rothdu/EEE4113F-Group13-2024/final-report/FrontMatter/Title.tex

\thispagestyle{empty}
\begin{center}
    
\Huge

\vspace{5cm}

% Title
EEE4113F 2024 Final Report \\
Red-winged Starling Nest Monitoring System

\vspace{2.5cm}

% UCT logo
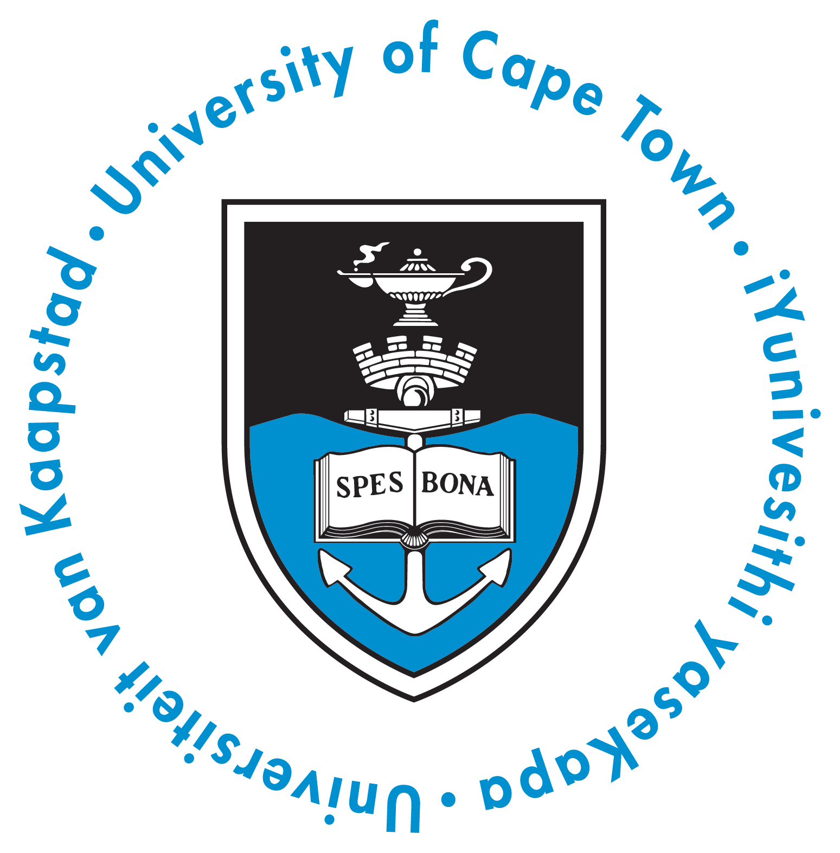
[picture p15: final-report/FrontMatter/UCT_logo.png]


\vfill

% My name
\large
\textbf{Prepared by:}\\
\textit{Group 13} \\
Ruviel Perumal - Power\\
Thiyashan Pillay - Electronic hardware \\
Robert Dugmore - Firmware\\
Mathapelo Morobi - Mechanical casing\\

\vspace{1cm}

% My supervisor's name
\textbf{Prepared for:}\\
EEE4113F\\
Department of Electrical Engineering\\
University of Cape Town

\vspace{2cm}

% Today's date
\today

% To add keywords?
% \vspace{2cm}
% \textbf{Keywords:} Keywords here

\end{center}
