rothdu/EEE4113F-Group13-2024/final-report/FrontMatter/Abstract.tex

\documentclass[class=report,11pt,crop=false]{standalone}
\input{../Style/ChapterStyle.tex}
\input{../FrontMatter/Glossary.tex}
\begin{document}
% \afterpage{
% \newgeometry{margin=30mm}
\chapter*{Abstract}

\ifstandalone
% \bibliography{../Bibliography/References.bib}
% \printnoidxglossary[type=\acronymtype,nonumberlist]
\fi
\end{document}
