rothdu/EEE4113F-Group13-2024/final-report/FrontMatter/Acknowledgements.tex

\documentclass[class=report,11pt,crop=false]{standalone}
\input{../Style/ChapterStyle.tex}
\begin{document}
\chapter*{Acknowledgements}
% \epigraph{No man is an island entire of itself; every man is a piece of the continent, a part of the main.}%
    % {\emph{---John Donne}}
% \vspace{0.3cm}

% Financial

% Academic

% Friends

% Family

\end{document}
