rothdu/EEE4113F-Group13-2024/final-report/Main.tex

% !TeX root = Main.tex

\documentclass[11pt]{report}
\input{Style/ChapterStyle.tex}
\usepackage{standalone} % Best loaded last in the preamble

% \input{FrontMatter/Glossary.tex}

\begin{document}

\pagenumbering{roman}
\input{FrontMatter/Title.tex}
\input{FrontMatter/Declaration.tex}
% \input{FrontMatter/Acknowledgements.tex}
% \input{FrontMatter/Abstract.tex}
\glsresetall

\tableofcontents
% \listoffigures

% \printnoidxglossary[type=\acronymtype,nonumberlist,title={Abbreviations}]
\newpage

\pagenumbering{arabic}

\input{Chapters/Introduction.tex}
\input{Chapters/Problem-analysis.tex}
\input{Chapters/Literature.tex}
\input{Chapters/Power.tex}
\input{Chapters/Hardware.tex}
\input{Chapters/Firmware.tex}
\input{Chapters/Mechanical.tex}
\input{Chapters/Conclusions.tex}
\input{Chapters/Recommendations.tex}

\newpage
\bibliography{Bibliography/References.bib}

\appendix
\input{Appendices/Appendix-A1.tex}
\input{Appendices/Appendix-B1.tex}

\end{document}
