rothdu/EEE4113F-Group13-2024/final-report/Chapters/Introduction.tex

% ----------------------------------------------------
% Introduction
% ----------------------------------------------------
\documentclass[class=report,11pt,crop=false]{standalone}
\input{../Style/ChapterStyle.tex}
\input{../FrontMatter/Glossary.tex}
\begin{document}
\chapter{Introduction \label{ch:introduction}}
% ----------------------------------------------------

\section{Background}
\section{Background}
The FitzPatrick Institute of African Ornithology falls within the Department of Biological Sciences at the University of Cape Town (UCT) in South Africa. It is a non-profit organisation that established it’s affiliation with UCT in September 1959. The main aim of FitzPatrick is to deepen understanding of avian life and to establish a permanent repository for ornithological data and materials crucial for research. They serve as pioneers and are one of the leading institutes when it comes to the studies of birds in the Southern Hemisphere.
\newline

The FitzPatrick Institute is also committed to training the next generation of ornithologists and conservationists. It offers undergraduate and postgraduate programs in ornithology, providing students with hands-on research experience and mentorship from leading experts in the field.
\newline

Overall, the FitzPatrick Institute of African Ornithology stands as a beacon of excellence in avian research and conservation, contributing valuable insights to our understanding of bird biology and ecology while working tirelessly to ensure the continued survival of Africa's avian biodiversity.
\newline

In 2017, the FitzPatrick initiated the Red-winged Starling Urban Ecology Project. The Red-winged starling, scientifically termed Onychognathus morio, is a notable bird within the Sturnidae family, endemic to eastern Africa from Ethiopia to South Africa's Cape region. For this specific project, we worked with Sally, who does her research on these starling birds.
\newline

Her main problems along her researching career were not being able to understand exactly what is going on in these nests of the Starling birds. Hence, her need for a camera trap device so that she can have more accurate and efficient data.

%%\section{Objectives}

%%\section{System Requirements}

\section{Scope \& Limitations}
The project focused on developing a remote surveillance system for the Starlings bird population at the University of Cape Town (UCT), which was divided into four main subsections: Power, Hardware, Firmware, and Mechanical Casing. the project aimed to develop a technological design to assist in wildlife data collection and conservation. This endeavour involved a collaborative effort including various engineering disciplines and leveraging the vast knowledge and research capabilities of the Fitz Patrick Institute.
\newline
Over 7 weeks, the project encompassed stakeholder engagement for gathering requirements, the design process, iterative improvements, and thorough testing. Material procurement was conducted from limited electronics online stores, with shipping days taking long and physical visits to outlets like BUCO for items not available online. A budget of R2000 was allocated to ensure a cost-effective solution.
\newline

In the subsequent chapters, the design processes of each submodule will be explained, showcasing diverse expertise and innovative solutions tailored to the unique requirements of monitoring the Starlings bird population. 

\section{Report Outline}
The report will proceed in a structured manner to provide a comprehensive analysis and solution to the identified problem. Beginning with the Introduction, the report will establish the context and significance of the problem, setting the stage for subsequent chapters. Following this, the Problem Analysis section will delve into a detailed examination of the identified issue, analysing its implications and significance within the relevant context.
\newline

Subsequently, a Literature Review will be conducted to draw upon existing research and scholarly work related to the problem statement. This review will serve to establish a theoretical framework and deepen understanding of the topic. Moving forward, chapters dedicated to Power, Hardware, Mechanical, and Firmware will follow. Each chapter will offer an overview of its respective aspect, analysing requirements, considerations, and design strategies pertinent to the solution.
\newline

The Conclusions section will summarise key findings and insights drawn from the analysis, offering recommendations for future actions and areas of further research. References will be provided to acknowledge and cite sources utilized throughout the report.
\newline
Finally, the report includes two appendices. Appendix A, the main appendix, contain supplementary information, data, or detailed analyses to support the main body of the report. Appendix B, consists of the GAs completed by each member of Group 13.

% ----------------------------------------------------
\ifstandalone
\bibliography{../Bibliography/References.bib}
\printnoidxglossary[type=\acronymtype,nonumberlist]
\fi
\end{document}
% ----------------------------------------------------
