rothdu/EEE4113F-Group13-2024/final-report/FrontMatter/Declaration.tex

{
\onehalfspacing
   
% Please leave the declaration as it is (Standard UCT declaration).
\chapter*{Declaration}
% \hrule

\vskip 10mm
\begin{enumerate}
\item I know that plagiarism is wrong. Plagiarism is to use another's work and pretend that it is one's
own.
\item I have used the IEEE convention for citation and referencing. Each contribution to, and quotation in,
this report from the work(s) of other people has been attributed, and has been cited and
referenced.
\item This report is my own work.
\item I have not allowed, and will not allow, anyone to copy my work with the intention of passing it off
as their own work or part thereof.
\end{enumerate}
\vskip 30mm

%signatures
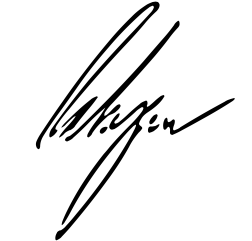
[picture p16: final-report/signatures/DGMROB001.png]
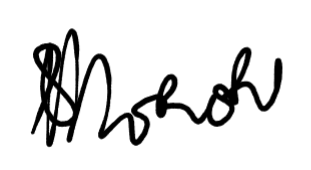
[picture p17: final-report/signatures/MRBMAT004.png]
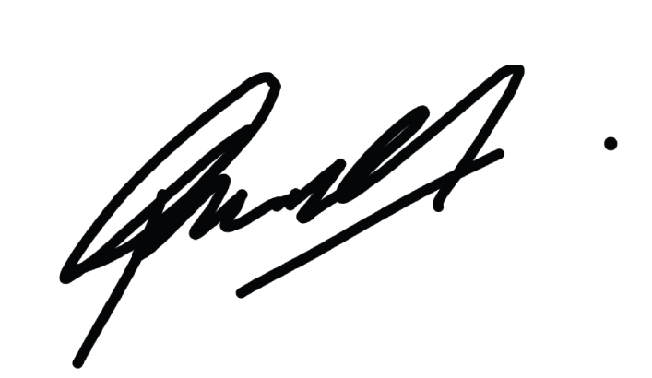
[picture p18: final-report/signatures/PRMRUV001.png]
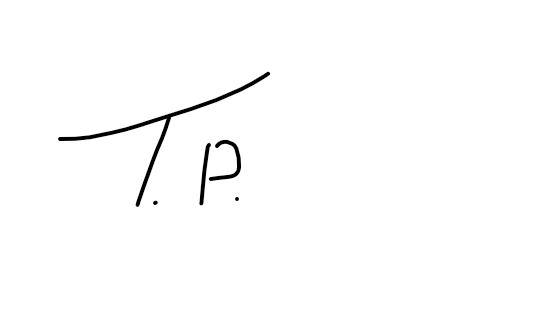
[picture p19: final-report/signatures/PLLTHI032.png]
\par\noindent\makebox[1.3in]{}\hfill\makebox[1.3in]{}\hfill\makebox[1.2in]{}\hfill\makebox[1.3in]{}%

%lines
\par\noindent\makebox[1.3in]{\hrulefill}\hfill\makebox[1.3in]{\hrulefill}\hfill\makebox[1.3in]{\hrulefill}\hfill\makebox[1.3in]{\hrulefill}%

%names
\par\noindent\makebox[1.3in][c]{Robert Dugmore}\hfill\makebox[1.3in][c]{Mathapelo Morobi}\hfill\makebox[1.3in][c]{Ruviel Perumal}\hfill\makebox[1.3in][c]{Thiyashan Pillay}

\vskip 20mm

%date
\par\noindent\makebox[1.3in]{\today}
\par\noindent\makebox[1.3in]{\hrulefill}
\par\noindent\makebox[1.3in][c]{Date}

% use for single signature:
% \par\noindent\makebox[2.0in]{\includegraphics[width=0.2\linewidth]{signatures/DGMROB001.png}}\hfill\makebox[2.0in]{\today}%
% \par\noindent\makebox[2.0in]{\hrulefill} \hfill\makebox[2.0in]{\hrulefill}%
% \par\noindent\makebox[2.0in][l]{Robert Dugmore}      \hfill\makebox[2.0in][l]{Date}%

}
