rothdu/EEE4113F-Group13-2024/final-report/Images/ESP-flow.png

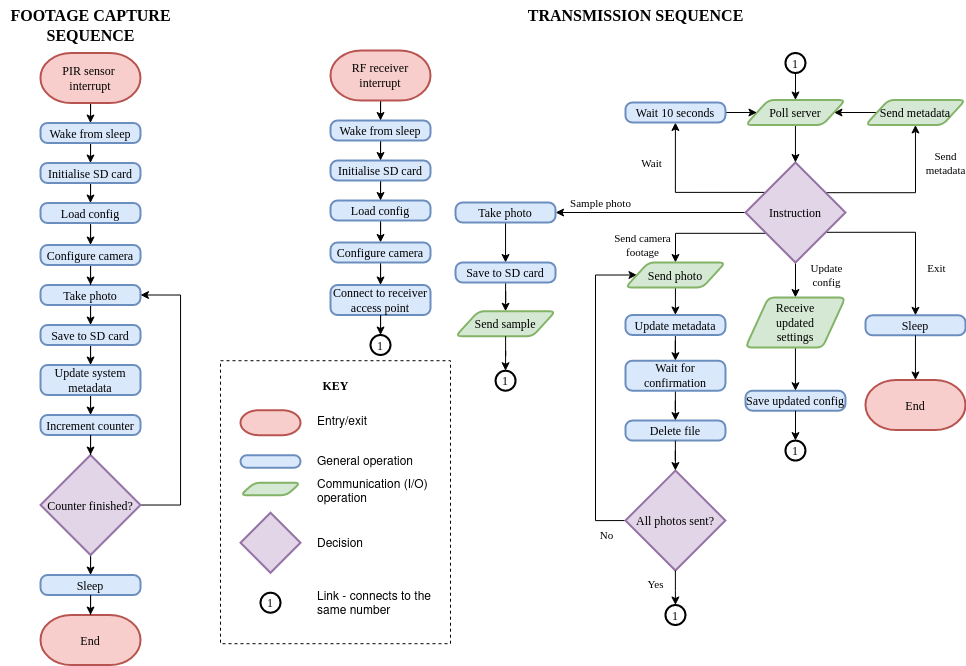
final-report/Images/ESP-flow.png
