rothdu/EEE4113F-Group13-2024/final-report/Images/flowchart.png

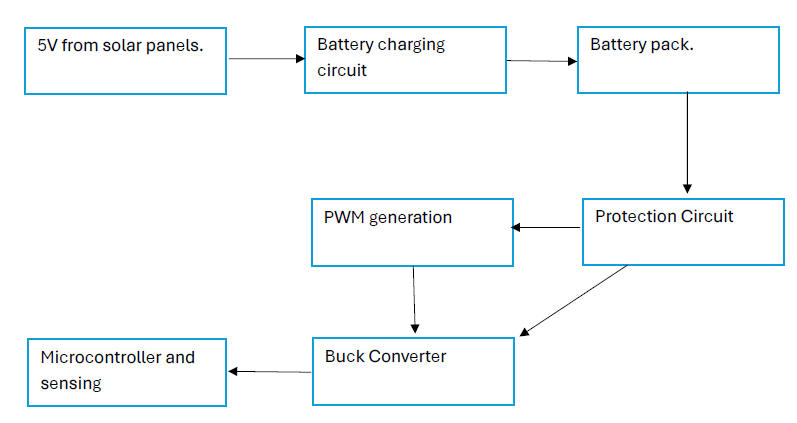
final-report/Images/flowchart.png
