rothdu/EEE4113F-Group13-2024/final-report/Images/nest.png

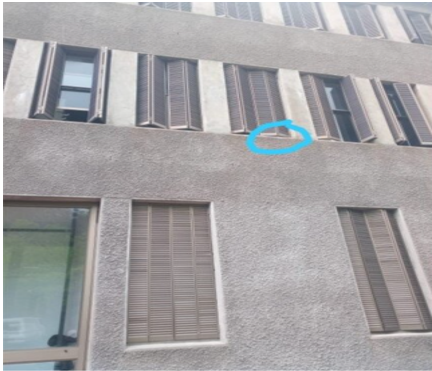
final-report/Images/nest.png
