rothdu/EEE4113F-Group13-2024/final-report/Images/sample-image-firmware.jpeg

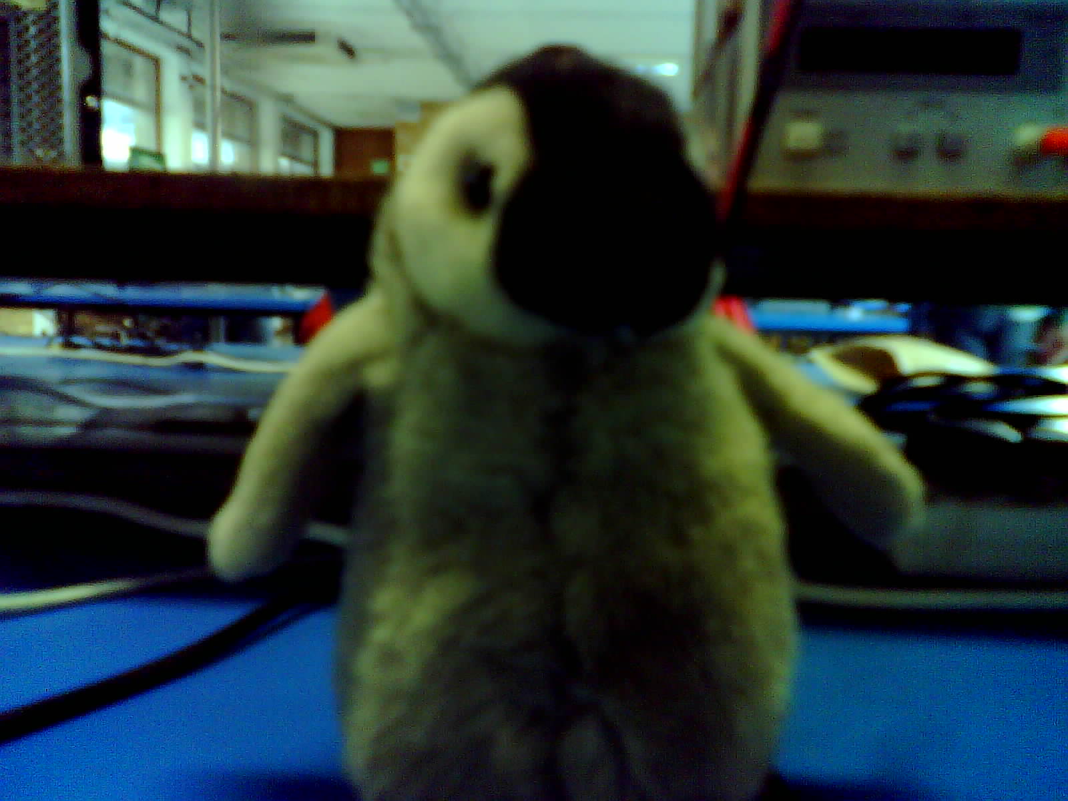
final-report/Images/sample-image-firmware.jpeg
