rothdu/EEE4113F-Group13-2024/final-report/Images/sensor_ss.png

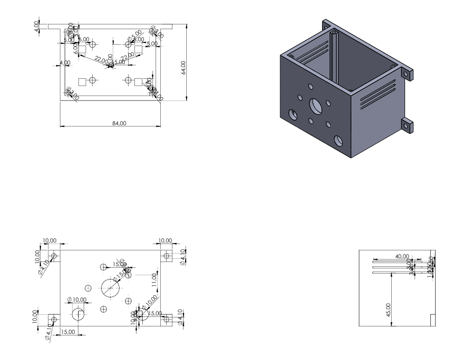
final-report/Images/sensor_ss.png
