rothdu/EEE4113F-Group13-2024/final-report/Images/stakeholdermap.jpeg

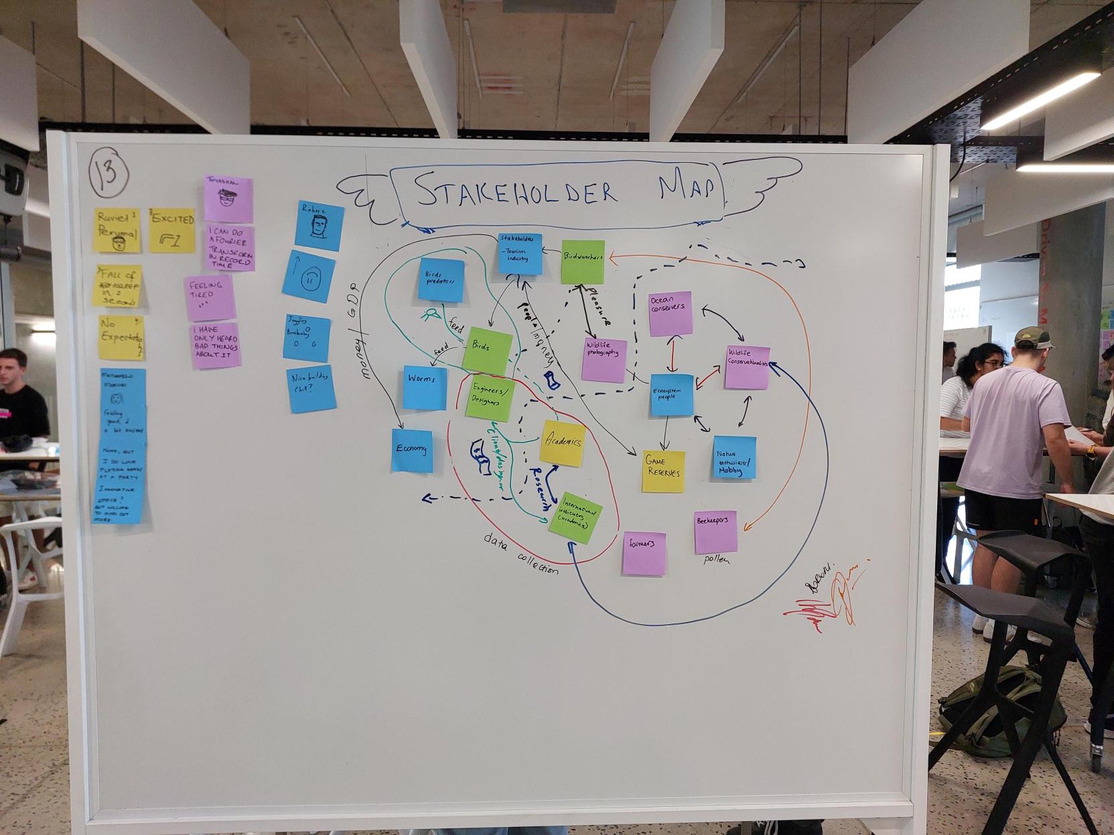
final-report/Images/stakeholdermap.jpeg
