rothdu/EEE4113F-Group13-2024/final-report/Images/ui.jpeg

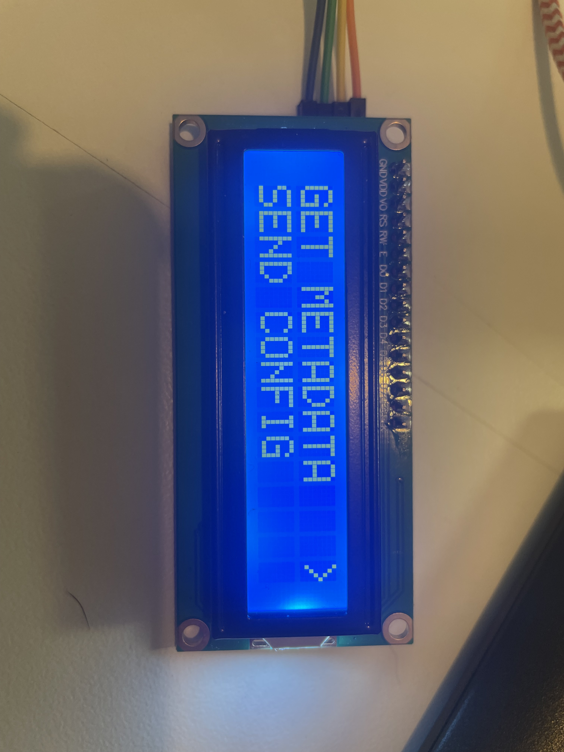
final-report/Images/ui.jpeg
