rothdu/EEE4113F-Group13-2024/sample-photos/2.jpeg

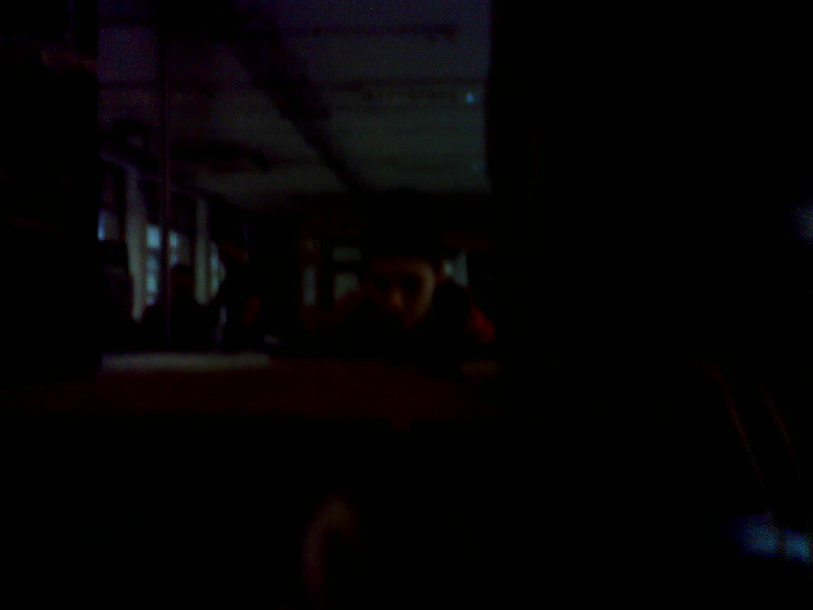
sample-photos/2.jpeg
