rothdu/EEE4113F-Group13-2024/sample-photos/3.jpeg

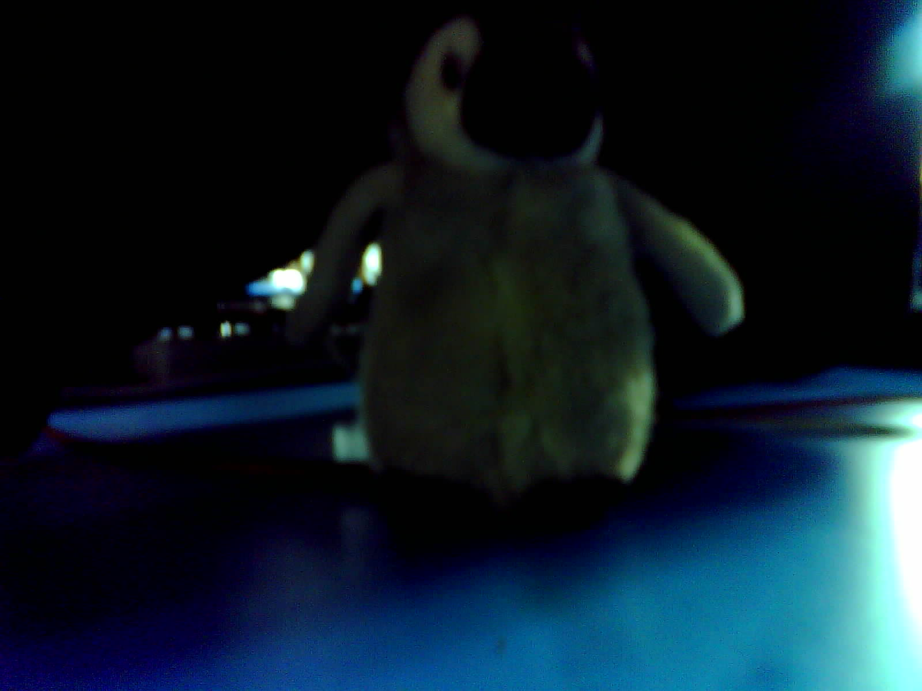
sample-photos/3.jpeg
