rothdu/EEE4113F-Group13-2024/circuit-schematics/LDR_Circuit.asc

LDR: res; 18k
M1: nmos
R1: res; 22k
R2: res; 22k
R3: res; 22k
R4: res; 3.3k
R5: res; 22k
U1: opamp2; LM358
V1: voltage; 5
V2: voltage; 3.3
Named nets: Out, 0, V++, VCC, Vin
.lib lm358.lib
.tran 0.01
