rothdu/EEE4113F-Group13-2024/circuit-schematics/LED_Circuit.asc

D1: LED
D2: LED
D3: LED
D4: LED
D5: LED
Q1: npn; 2N2222
R1: res; 10k
R2: res; 18k
R3: res; 15
R4: res; 280
V1: voltage; 5
V2: voltage; 3.3
V3: voltage; 5V
Named nets: 0
.tran 10
