rothdu/EEE4113F-Group13-2024/circuit-schematics/PNP_Switch.asc

Q1: pnp; 2N2907
R1: res; 1k
R2: res; 10k
R3: res; 22k
Named nets: 0, Out, ESP_In, Sensor_In
.tran 1
