rothdu/EEE4113F-Group13-2024/circuit-schematics/EEE4113F_Power_Submodule_Group13.kicad_sch

## KiCad design circuit-schematics/EEE4113F_Power_Submodule_Group13.kicad_sch (2024-05-12)

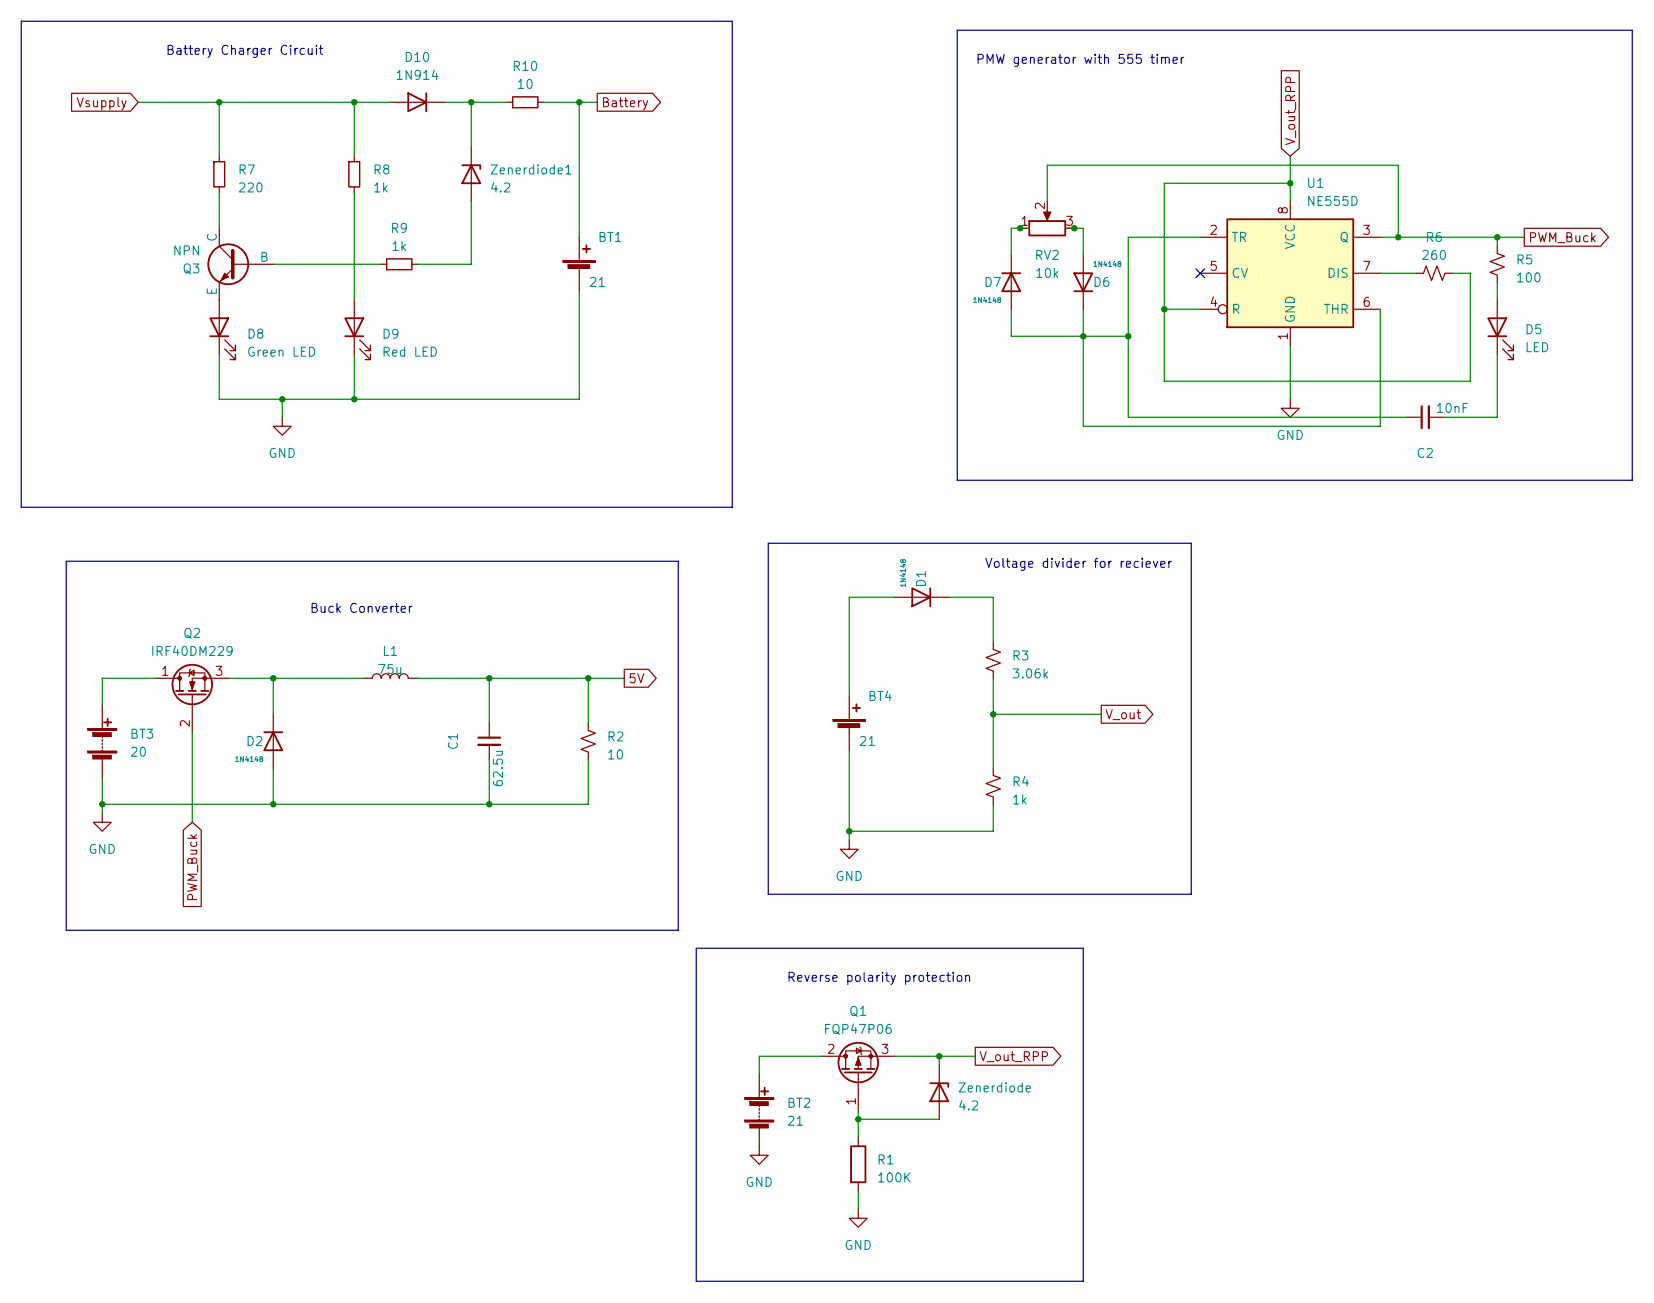
[picture p35: schematic EEE4113F_Power_Submodule_Group13.kicad_sch]

Parts:
BT1, BT2, BT4: 21
BT3: 20
C1: 62.5u
C2: 10nF
D1, D2, D6, D7: 1N4148; D_DO-35_SOD27_P7.62mm_Horizontal
D5: LED
D8: Green LED
D9: Red LED
D10: 1N914; D_DO-35_SOD27_P7.62mm_Horizontal
L1: 75u
Q1: FQP47P06; TO-220-3_Vertical
Q2: IRF40DM229; DirectFET_MF
Q3: NPN
R1: 100K
R2, R10: 10
R3: 3.06k
R4, R8, R9: 1k
R5: 100
R6: 260
R7: 220
RV2: 10k
U1: NE555D; SOIC-8_3.9x4.9mm_P1.27mm
Zenerdiode, Zenerdiode1: 4.2

Connections:
5V: C1.1, L1.2, R2.1
Battery: BT1.1 (+), R10.2
GND: BT1.2 (-), BT2.2 (-), BT3.2 (-), BT4.2 (-), C1.2, D2.2 (A), D8.1 (K), D9.1 (K), R1.2, R2.2, R4.2, U1.1 (GND)
unnamed: BT2.1 (+), Q1.2 (D)
unnamed: BT3.1 (+), Q2.1 (D)
unnamed: BT4.1 (+), D1.2 (A)
unnamed: C2.1, D6.1 (K), D7.2 (A), U1.2 (TR), U1.6 (THR)
unnamed: C2.2, D5.1 (K)
unnamed: D1.1 (K), R3.1
unnamed: D2.1 (K), L1.1, Q2.3 (S)
unnamed: D5.2 (A), R5.2
unnamed: D6.2 (A), RV2.3
unnamed: D7.1 (K), RV2.1
unnamed: D8.2 (A), Q3.3 (E)
unnamed: D9.2 (A), R8.2
unnamed: D10.1 (K), R10.1, Zenerdiode1.1 (K)
unnamed: Q1.1 (G), R1.1, Zenerdiode.2 (A)
unnamed: Q3.1 (C), R7.2
unnamed: Q3.2 (B), R9.1
unnamed: R6.1, U1.7 (DIS)
unnamed: R9.2, Zenerdiode1.2 (A)
PWM_Buck: Q2.2 (G), R5.1, RV2.2, U1.3 (Q)
V_out: R3.2, R4.1
V_out_RPP: Q1.3 (S), R6.2, U1.4 (R), U1.8 (VCC), Zenerdiode.1 (K)
Vsupply: D10.2 (A), R7.1, R8.1

Notes on the sheet:
Voltage divider for reciever
Buck Converter
PMW generator with 555 timer
Battery Charger Circuit
Reverse polarity protection
